lsd-maddrive/mishanya-bot-project/docs/schemes.png

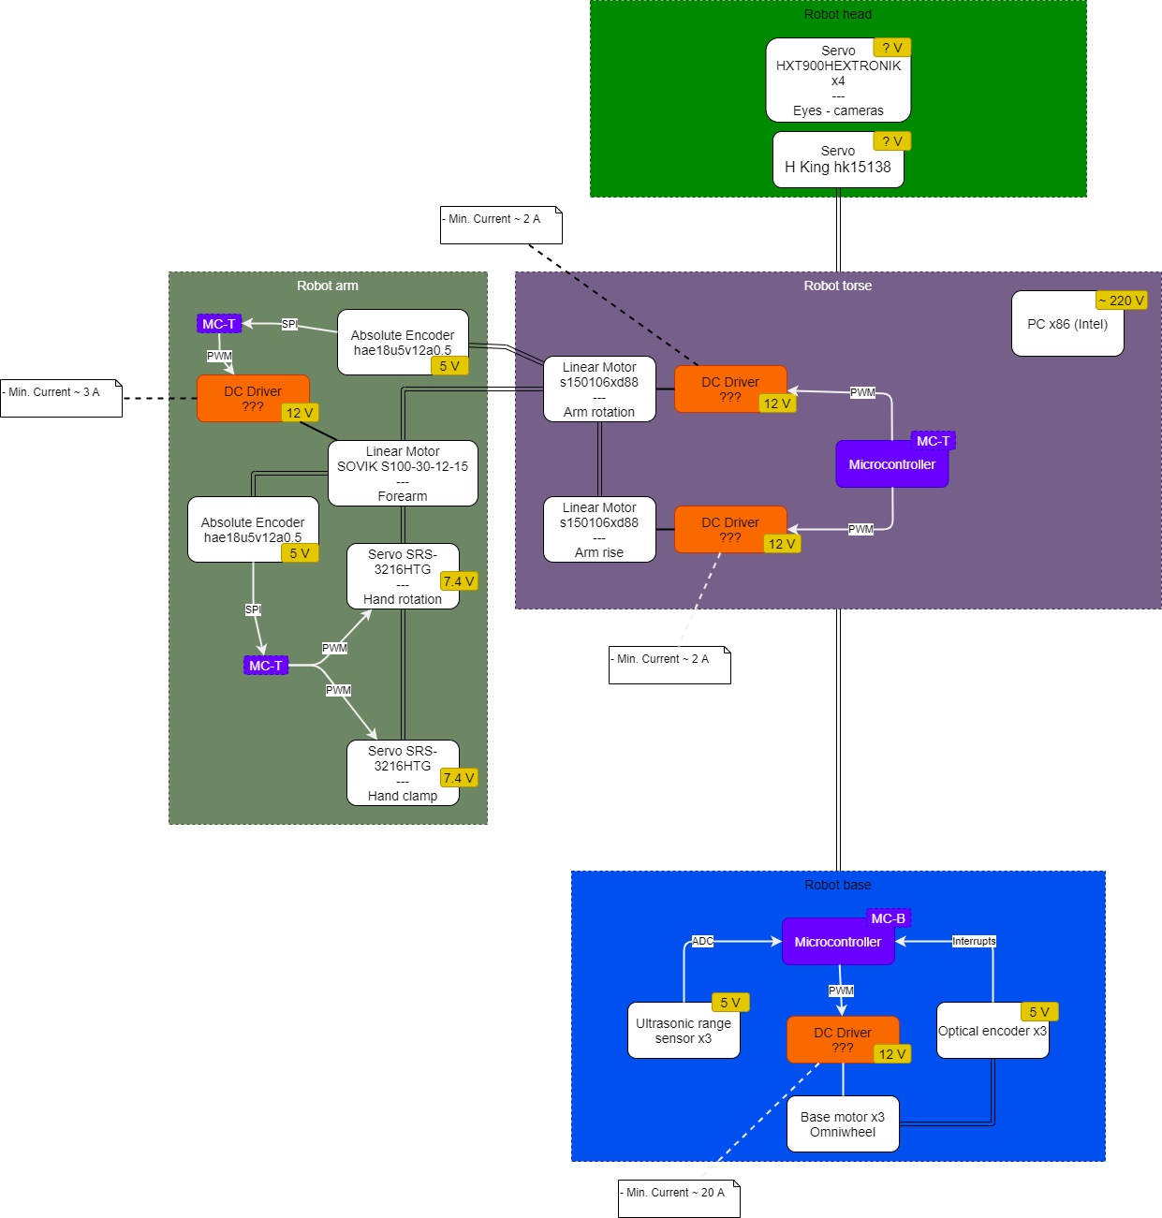
docs/schemes.png
