lsd-maddrive/mishanya-bot-project/firmware/src/lld_red_driver.c

#include <lld_red_driver.h>

/**
 * @details initialize bridge driver type red
 * @param[in] pins - pointer to the struct of control pins
 * @param[in] pwm_ctx - pointer to the structure of PWM config
 */
void lld_red_init_driver(const line_driver_t* pins, const pwm_ctx_t* pwm_ctx)
{

  palSetLineMode(pins->hin_1, PAL_MODE_ALTERNATE(pwm_ctx->pwm_ch.alt_func_1));

  palSetLineMode(pins->lin_2, PAL_MODE_OUTPUT_PUSHPULL);
  palSetLineMode(pins->lin_1, PAL_MODE_OUTPUT_PUSHPULL);

}

/**
 * @details the function open bridge driver in first direction
 * @param[in] control - pointer to the control struct of driver
 * @param[in] pwm_ch - pointer to the structure of PWM channel
 * @param[in] period - PWM period
 */
void lld_red_driver_direct(const control_driver_t* control, const pwm_channel_t* pwm_ch, uint16_t period)
{

	palWriteLine(control->line_control.lin_1, PAL_LOW);
	palWriteLine(control->line_control.lin_2, PAL_HIGH);
	pwmEnableChannel(control->pwm_setting_ctx.driver_ptr, pwm_ch->ch_pwm_1, period);

}

/**
 * @details the function open bridge driver in reverse direction
 * @param[in] control - pointer to the control struct of driver
 * @param[in] pwm_ch - pointer to the structure of PWM channel
 * @param[in] period - PWM period
 */
void lld_red_driver_reverse(const control_driver_t* control, const pwm_channel_t* pwm_ch, uint16_t period)
{

	palWriteLine(control->line_control.lin_1, PAL_HIGH);
	palWriteLine(control->line_control.lin_2, PAL_LOW);
	pwmEnableChannel(control->pwm_setting_ctx.driver_ptr, pwm_ch->ch_pwm_1, period);

}

/**
 * @details the function disables the selected direction
 * @param[in] control - pointer to the control struct of driver
 * @param[in] pwm_ch - pointer to the structure of PWM channel
 */
void lld_red_driver_off(const control_driver_t* control, const pwm_channel_t* pwm_ch)
{

	palWriteLine(control->line_control.lin_1, PAL_LOW);
	palWriteLine(control->line_control.lin_2, PAL_LOW);
	pwmDisableChannel(control->pwm_setting_ctx.driver_ptr, pwm_ch->ch_pwm_1);

}
