lsd-maddrive/mishanya-bot-project/firmware/Base/include/i2c.h

#ifndef BASE_I2C_H
#define BASE_I2C_H

#include "common.h"
#include "cnfg_peripherals.h"

/**
 * brief stop i2c
 */
void i2cStopDriver(void);

/**
 * brief start i2c and init pins
 */
void initI2C(void);

/**
 * @brief   Write multiple bytes of data from slave
 * @param
 *          address         7 bit address of slave device
 *          txbuf           link to a buffer array with data to write
 *          length          number of bytes to write
 *          timeout         timeout value [ms]
 *
 * @return                  The operation status.
 * @retval  MSG_OK          if the function succeeded.
 * @retval  MSG_RESET       if one or more I2C errors occurred, the errors can
 *                          be retrieved using @p i2cGetErrors().
 * @retval  MSG_TIMEOUT     if a timeout occurred before operation end.
 */
msg_t i2cSimpleWrite(uint8_t address, uint8_t *txbuf, uint8_t length, uint16_t timeout);

/**
 * @brief   Read multiple bytes of data from slave
 *
 * @param
 *          address         7 bit address of slave device
 *          rxbuf           link to a buffer array where to store read data
 *          length          number of bytes to read
 *          timeout         timeout value [ms]
 *
 * @return                  The operation status.
 * @retval  MSG_OK          if the function succeeded.
 * @retval  MSG_RESET       if one or more I2C errors occurred, the errors can
 *                          be retrieved using @p i2cGetErrors().
 * @retval  MSG_TIMEOUT     if a timeout occurred before operation end.
 */
msg_t i2cSimpleRead(uint8_t address, uint8_t *rxbuf, uint8_t length, uint16_t timeout);

/**
 * @brief   Read multiple bytes of data from specific register of slave
 * @details Function writes register address data to slave and then performs
 *          repeated start action with read bit set
 * @param
 *          address         7 bit address of slave device
 *          register_addr   address of register to read
 *          rxbuf           link to a buffer array where to store read data
 *          length          number of bytes to read
 *          timeout         timeout value [ms]
 *
 * @return                  The operation status.
 * @retval  MSG_OK          if the function succeeded.
 * @retval  MSG_RESET       if one or more I2C errors occurred, the errors can
 *                          be retrieved using @p i2cGetErrors().
 * @retval  MSG_TIMEOUT     if a timeout occurred before operation end.
 */
msg_t i2cRegisterRead(uint8_t address, uint8_t register_addr, uint8_t *rxbuf, uint8_t length, uint16_t timeout);


#endif //BASE_I2C_H
